jason-watkins/nixie-clock/docs/design_analysis/main.tex

\documentclass[11pt,letterpaper]{article}

% ---------------------------------------------------------------------------
% Nixie Clock -- Design Basis
%
% Derives the board's key electrical characteristics from first principles
% and from component datasheets on file in docs/datasheets/. This document
% works at the schematic level only; it is the source from which the
% eventual Hardware User Guide's tables are extracted.
% ---------------------------------------------------------------------------

\usepackage[letterpaper,margin=1in]{geometry}

% Project-local fonts (PT Serif for text, IBM Plex Mono for monospace; both
% carry Latin and Cyrillic, are OFL-licensed, and are committed under fonts/ so
% the build has no system-font dependency). Requires XeLaTeX or LuaLaTeX --
% fontspec does not work under pdfLaTeX.
\usepackage{fontspec}
\setmainfont{PTSerif}[
  Path = fonts/,
  Extension = .ttf,
  UprightFont = *-Regular,
  BoldFont = *-Bold,
  ItalicFont = *-Italic,
  BoldItalicFont = *-BoldItalic,
]
% Plex Mono sets a shade larger than PT Serif at the same nominal size;
% MatchLowercase equalises the x-heights, trimming about 3 percent, so inline
% \texttt does not read oversized against the surrounding text.
\setmonofont{IBMPlexMono}[
  Path = fonts/,
  Extension = .ttf,
  UprightFont = *-Regular,
  BoldFont = *-Bold,
  Scale = MatchLowercase,
]

\usepackage{amsmath,amssymb}
\usepackage{siunitx}
\usepackage{booktabs}
\usepackage{longtable}
\usepackage{array}
\usepackage{multirow}
\usepackage{graphicx}
\usepackage{enumitem}
\usepackage[colorlinks=true,linkcolor=blue,citecolor=blue,urlcolor=blue]{hyperref}
\usepackage{cleveref}
\usepackage{chngcntr}

% Tables number "<section>-<n>" (e.g. 2-1, 2-2, 3-1), resetting only at
% each \section, not at \subsection -- a table living inside a particular
% subsection is incidental to this scheme, not what it counts by.
\counterwithin{table}{section}
\renewcommand{\thetable}{\thesection-\arabic{table}}
\counterwithin{figure}{section}
\renewcommand{\thefigure}{\thesection-\arabic{figure}}

\graphicspath{{figures/}}

% Reference designators are set the way the schematics draw them: a class
% letter carrying a subsystem-and-function tag as an upright subscript.
% \des{R}{3V3D1} -> R_3V3D1. Works in prose and inside math alike, and
% degrades to a flat "R_3V3D1" in PDF bookmarks, where math is unavailable.
\newcommand{\des}[2]{\texorpdfstring{\ensuremath{#1_{\mathrm{#2}}}}{#1\_#2}}

% Number down to \paragraph (depth 4) so a deeply nested topic -- e.g. one
% pin's check inside a "housekeeping" subsubsection -- still gets its own
% citable number instead of forcing an ever-larger subsubsection to do the
% job of several independent ones. article's default tocdepth already
% reaches this depth, so paragraph headings appear in the ToC too.
\setcounter{secnumdepth}{4}
\crefname{paragraph}{paragraph}{paragraphs}
\Crefname{paragraph}{Paragraph}{Paragraphs}

\sisetup{
  per-mode = symbol,
  detect-all = true,
  table-align-text-post = false,
}

% Consistent units used throughout
\DeclareSIUnit\decade{decade}

% Shorthand for a datasheet citation inside table cells and prose.
% Usage: \ds{SN74141\_TI.pdf}{2}
\newcommand{\ds}[2]{\textit{#1}, p.~#2}

\newcolumntype{L}[1]{>{\raggedright\arraybackslash}p{#1}}

% \DesignRev is generated by scripts/make_release.py --sync-doc-rev from
% the KiCad project's REV text variable -- do not hand-edit revision.tex.
\input{revision}

\title{Nixie Clock: Design Basis}
\author{}
\date{Rev \DesignRev{}, compiled \today}

\begin{document}
\maketitle

\begin{abstract}
\noindent
This document derives the main electrical characteristics of the Nixie Clock
board. It uses component datasheets and circuit analysis. The analysis applies
at the schematic level. Package data applies only when a part is available in
one package. Each numerical value for a critical component has a datasheet
reference in \texttt{docs/datasheets/}. Other component values use standard
engineering practice. The analysis starts at the Nixie-tube load. It then
derives the 170~V, 5~V, and 3.3~V supplies. The final section derives the
USB-PD input stage.
\end{abstract}

\tableofcontents
\listoftables
\listoffigures

\input{sections/01_introduction}
\input{sections/02_tubes}
\input{sections/03_bcd_driver}
\input{sections/04_hv_components}
\input{sections/05_hv_converter}
\input{sections/06_lv_components}
\input{sections/07_esp32}
\input{sections/08_5v_converter}
\input{sections/09_3v3_converter}
\input{sections/10_usb_pd}

\end{document}
