jason-watkins/nixie-clock/docs/design_analysis/schematics/3v3.kicad_sch

## KiCad design docs/design_analysis/schematics/3v3.kicad_sch (2026-07-31)

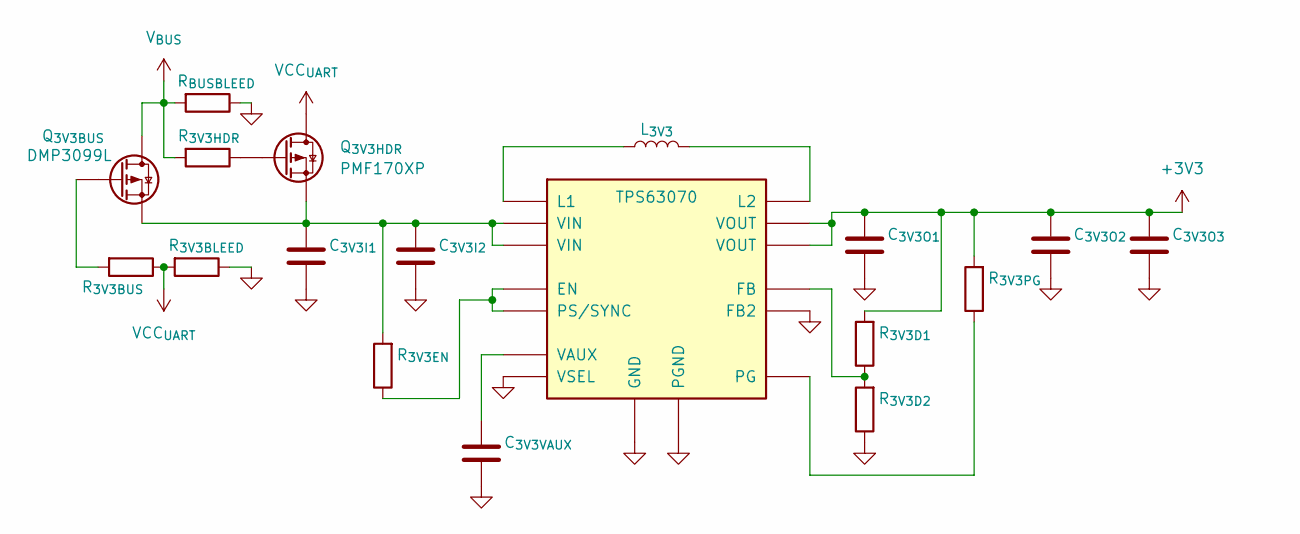
[picture p26: schematic 3v3.kicad_sch]

Parts:
C_{3V3I1}: 10uF; C_0805_2012Metric; MFG Part No CL21A106KAYNNNE; LCSC C15850
C_{3V3I2}: 10uF; C_0603_1608Metric; MFG Part No CL10A106MA8NRNC; LCSC C96446
C_{3V3O1}: 10uF; C_0603_1608Metric; MFG Part No CL10A226MQ8NRNC; LCSC C59461
C_{3V3O2}: 22uF; C_1206_3216Metric; MFG Part No CL31A226KPHNNNE; LCSC C5672
C_{3V3O3}: 47uF; C_1206_3216Metric; MFG Part No CL31A476MPHNNNE; LCSC C96123
C_{3V3VAUX}: 100nF; C_0402_1005Metric; MFG Part No CL05B104KO5NNNC; LCSC C1525
L_{3V3}: 1.5uH; L_Bourns_SRN5040TA; MFG Part No SRN5040TA-1R5M
Q_{3V3BUS}: DMP3099L; SOT-323_SC-70; MFG Part No PMF170XP,115
Q_{3V3HDR}: PMF170XP; SOT-323_SC-70; MFG Part No PMF170XP,115
R_{3V3BLEED}, R_{3V3BUS}, R_{3V3HDR}, R_{3V3PG}: 100k; R_0402_1005Metric; MFG Part No 0402WGF1003TCE; LCSC C25741
R_{3V3D1}: 120k; R_0402_1005Metric; MFG Part No 0402WGF1203TCE; LCSC C25750
R_{3V3D2}: 39k; R_0402_1005Metric; MFG Part No 0402WGF5102TCE; LCSC C25794
R_{3V3EN}: 10k; R_0402_1005Metric; MFG Part No 0402WGF1002TCE; LCSC C25744
R_{BUSBLEED}: 100k; R_0402_1005Metric; MFG Part No 0402WGF1003TCE; LCSC C25741
U302: TPS63070; VQFN-15_2.5x3mm_TI_RNM0015A; MFG Part No TPS630702RNMR

Connections:
+3V3: C_{3V3O1}.1, C_{3V3O2}.1, C_{3V3O3}.1, R_{3V3D1}.2, R_{3V3PG}.2, U302.7 (VOUT), U302.8 (VOUT)
GND: C_{3V3I1}.2, C_{3V3I2}.2, C_{3V3O1}.2, C_{3V3O2}.2, C_{3V3O3}.2, C_{3V3VAUX}.2, R_{3V3BLEED}.1, R_{3V3D2}.1, R_{BUSBLEED}.1, U302.4 (GND), U302.6 (FB2), U302.10 (PGND), U302.15 (VSEL)
unnamed: C_{3V3I1}.1, C_{3V3I2}.1, Q_{3V3BUS}.2 (S), Q_{3V3HDR}.2 (S), R_{3V3EN}.2, U302.12 (VIN), U302.13 (VIN)
unnamed: C_{3V3VAUX}.1, U302.3 (VAUX)
unnamed: L_{3V3}.1, U302.11 (L1)
unnamed: L_{3V3}.2, U302.9 (L2)
unnamed: Q_{3V3BUS}.1 (G), R_{3V3BUS}.2
unnamed: Q_{3V3HDR}.1 (G), R_{3V3HDR}.1
unnamed: R_{3V3D1}.1, R_{3V3D2}.2, U302.5 (FB)
unnamed: R_{3V3EN}.1, U302.1 (PS/SYNC), U302.14 (EN)
unnamed: R_{3V3PG}.1, U302.2 (PG)
VCC_{UART}: Q_{3V3HDR}.3 (D), R_{3V3BLEED}.2, R_{3V3BUS}.1
V_{BUS}: Q_{3V3BUS}.3 (D), R_{3V3HDR}.2, R_{BUSBLEED}.2
