jason-watkins/nixie-clock/docs/design_analysis/schematics/5v.kicad_sch

## KiCad design docs/design_analysis/schematics/5v.kicad_sch (2026-07-29)

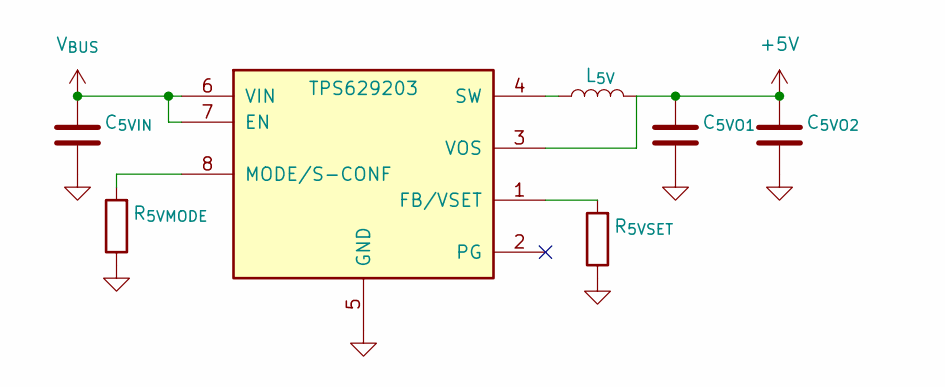
[picture p27: schematic 5v.kicad_sch]

Parts:
C_{5VIN}: 10uF; C_0805_2012Metric; MFG Part No CL21A106KAYNNNE; LCSC C15850
C_{5VO1}, C_{5VO2}: 22uF; C_1206_3216Metric; MFG Part No CL31A226KPHNNNE; LCSC C5672
L_{5V}: 2.2uH; L_Bourns_SRN5040TA; MFG Part No SRN5040TA-2R2M
R_{5VMODE}: 27k; R_0402_1005Metric; MFG Part No 0402WGF2702TCE; LCSC C25771
R_{5VSET}: 80.6k; R_0402_1005Metric; MFG Part No 0402WGF7502TCE; LCSC C25798
U303: TPS629203; SOT-583-8; MFG Part No TPS629203DRLR

Connections:
+5V: C_{5VO1}.1, C_{5VO2}.1, L_{5V}.2, U303.3 (VOS)
GND: C_{5VIN}.2, C_{5VO1}.2, C_{5VO2}.2, R_{5VMODE}.1, R_{5VSET}.1, U303.5 (GND)
unnamed: L_{5V}.1, U303.4 (SW)
unnamed: R_{5VMODE}.2, U303.8 (MODE/S-CONF)
unnamed: R_{5VSET}.2, U303.1 (FB/VSET)
V_{BUS}: C_{5VIN}.1, U303.6 (VIN), U303.7 (EN)
