jason-watkins/nixie-clock/docs/design_analysis/schematics/hv.kicad_sch

## KiCad design docs/design_analysis/schematics/hv.kicad_sch (2026-07-29)

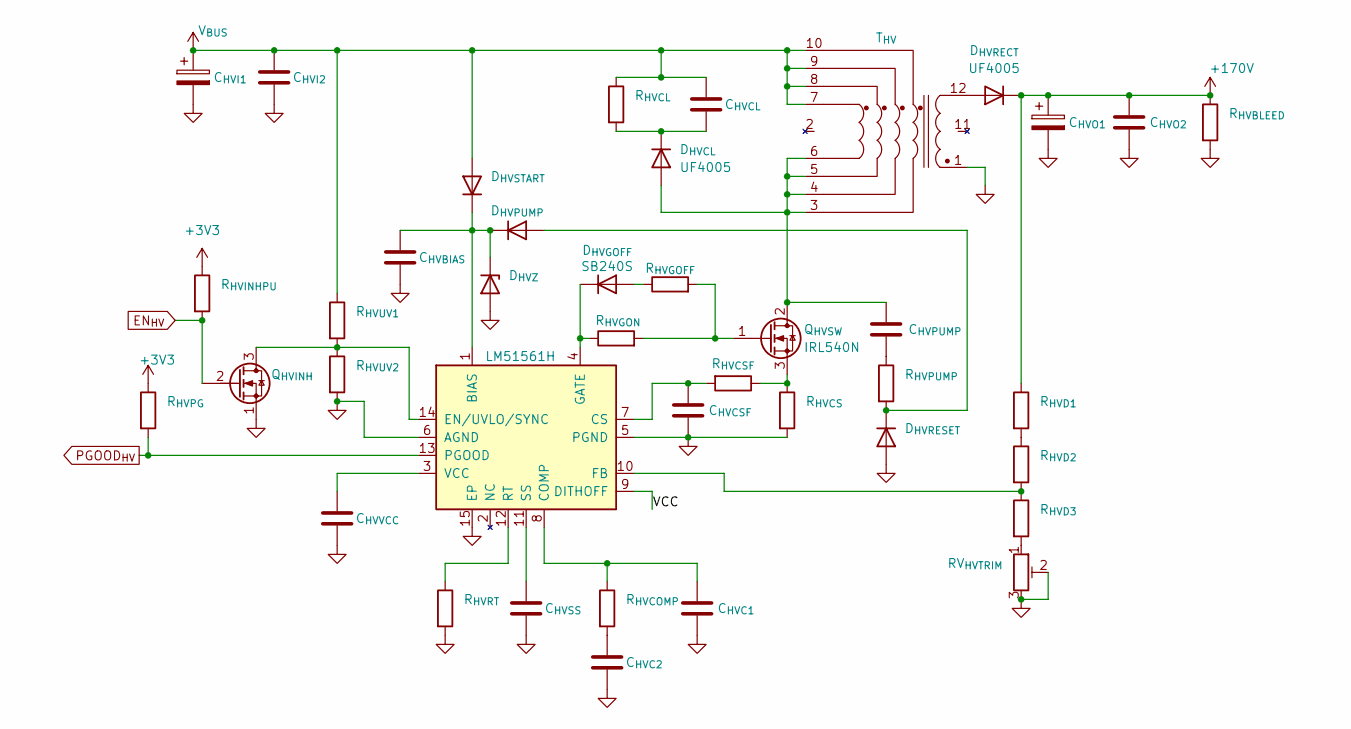
[picture p28: schematic hv.kicad_sch]

Parts:
C_{HVBIAS}: 1uF; C_Rect_L5.1mm_W3.2mm_P5.08mm_Goldmax; MFG Part No C322C103K5R5TA
C_{HVC1}: 220pF; C_Rect_L5.1mm_W3.2mm_P5.08mm_Goldmax; MFG Part No C322C221K5R5TA
C_{HVC2}: 100nF; C_Rect_L5.1mm_W3.2mm_P5.08mm_Goldmax; MFG Part No C322C104K5R5TA
C_{HVCL}: 12nF; C_Rect_L3.8mm_W2.5mm_P5.08mm_Goldmax; MFG Part No C317C123K1R5TA7301
C_{HVCSF}: 470pF; C_Rect_L3.8mm_W2.5mm_P2.54mm_Goldmax; MFG Part No C315C471K5R5TA
C_{HVI1}: 100uF; CP_Radial_D8.0mm_P3.50mm; MFG Part No A750KK107M1EAAE040
C_{HVI2}: 4.7uF; C_Rect_L5.1mm_W3.2mm_P5.08mm_Goldmax; MFG Part No C322C475K5R5TA
C_{HVO1}: 4.7uF; CP_Radial_D8.0mm_P3.50mm; MFG Part No A759KS475M2EAAE496
C_{HVO2}: 100nF; C_Rect_L7.9mm_W5.9mm_P5.00mm_ECQE; MFG Part No ECQ-E2104KB
C_{HVPUMP}: 4.7nF
C_{HVSS}: 220nF; C_Rect_L5.1mm_W3.2mm_P5.08mm_Goldmax; MFG Part No C322C224K5R5TA7301
C_{HVVCC}: 2.2uF; C_Rect_L5.1mm_W3.2mm_P5.08mm_Goldmax; MFG Part No C322C225K5R5TA
D_{HVCL}: UF4005; D_DO-41_SOD81_P7.62mm_Horizontal; MFG Part No UF4005
D_{HVGOFF}: SB240S; D_DO-41_SOD81_P7.62mm_Horizontal; MFG Part No SB240S-E3/54
D_{HVPUMP}: D
D_{HVRECT}: UF4005; D_DO-41_SOD81_P10.16mm_Horizontal; MFG Part No UF4005
D_{HVRESET}: D
D_{HVSTART}: D
D_{HVZ}: D_Zener
Q_{HVINH}: TN2106N3-G; TO-92L; MFG Part No TN2106N3-G
Q_{HVSW}: IRL540N; TO-220-3_Vertical; MFG Part No IRL540NPBF
RV_{HVTRIM}: 3296; Potentiometer_Bourns_3296W_Vertical; MFG Part No 3296W-1-202LF
R_{HVBLEED}: 1.5M; R_Axial_DIN0207_L6.3mm_D2.5mm_P7.62mm_Horizontal; MFG Part No MFR-25FBF52-1M5
R_{HVCL}: 30k; R_Axial_DIN0207_L6.3mm_D2.5mm_P7.62mm_Horizontal; MFG Part No MFR-25FRF52-30K
R_{HVCOMP}: 10k; R_Axial_DIN0207_L6.3mm_D2.5mm_P7.62mm_Horizontal; MFG Part No MFR-25FRF52-10K
R_{HVCSF}: 100; R_Axial_DIN0207_L6.3mm_D2.5mm_P7.62mm_Horizontal; MFG Part No MFR-25FBF52-100R
R_{HVCS}: 39m; R_2512_6332Metric_Pad1.40x3.35mm_HandSolder; MFG Part No TLRP3A20WR039FTE
R_{HVD1}, R_{HVD2}: 866k; R_Axial_DIN0207_L6.3mm_D2.5mm_P7.62mm_Horizontal; MFG Part No MFR-25FRF52-866K
R_{HVD3}: 8.87k; R_Axial_DIN0207_L6.3mm_D2.5mm_P7.62mm_Horizontal; MFG Part No MFR-25FBF52-8K87
R_{HVGOFF}: 3.3; R_Axial_DIN0207_L6.3mm_D2.5mm_P7.62mm_Horizontal; MFG Part No MFR-25FTE52-3R3
R_{HVGON}: 10; R_Axial_DIN0207_L6.3mm_D2.5mm_P7.62mm_Horizontal; MFG Part No MFR-25FBF52-10R
R_{HVINHPU}: 100k; R_Axial_DIN0207_L6.3mm_D2.5mm_P7.62mm_Horizontal; MFG Part No MFR-25FRF52-100K
R_{HVPG}: 100k; R_Axial_DIN0207_L6.3mm_D2.5mm_P7.62mm_Horizontal; MFG Part No MFR-25FRF52-100K
R_{HVPUMP}: 82
R_{HVRT}: 147k; R_Axial_DIN0207_L6.3mm_D2.5mm_P7.62mm_Horizontal; MFG Part No MFR-25FRF52-147K
R_{HVUV1}: 63.4k; R_Axial_DIN0207_L6.3mm_D2.5mm_P7.62mm_Horizontal; MFG Part No MFR-25FRF52-143K
R_{HVUV2}: 32.4k; R_Axial_DIN0207_L6.3mm_D2.5mm_P7.62mm_Horizontal; MFG Part No MFR-25FRF52-32K4
T_{HV}: DA2032-AL; MFG Part No DA2032-AL
U2: LM51561H; Texas_HTSSOP-14-1EP_4.4x5mm_P0.65mm_EP3.4x5mm_Mask3.155x3.2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; MFG Part No LM51561HPWPR

Connections:
+3V3: R_{HVINHPU}.1, R_{HVPG}.1
+170V: C_{HVO1}.1, C_{HVO2}.1, D_{HVRECT}.1 (K), R_{HVBLEED}.1, R_{HVD1}.1
EN_{HV}: Q_{HVINH}.2 (G), R_{HVINHPU}.2
GND: C_{HVBIAS}.1, C_{HVC1}.1, C_{HVC2}.1, C_{HVCSF}.1, C_{HVI1}.2, C_{HVI2}.2, C_{HVO1}.2, C_{HVO2}.2, C_{HVSS}.1, C_{HVVCC}.1, D_{HVRESET}.2 (A), D_{HVZ}.2 (A), Q_{HVINH}.1 (S), RV_{HVTRIM}.2, RV_{HVTRIM}.3, R_{HVBLEED}.2, R_{HVCS}.2, R_{HVRT}.2, R_{HVUV2}.2, T_{HV}.1, U2.5 (PGND), U2.6 (AGND), U2.15 (EP)
unnamed: C_{HVBIAS}.2, D_{HVPUMP}.1 (K), D_{HVSTART}.1 (K), D_{HVZ}.1 (K), U2.1 (BIAS)
unnamed: C_{HVC1}.2, R_{HVCOMP}.1, U2.8 (COMP)
unnamed: C_{HVC2}.2, R_{HVCOMP}.2
unnamed: C_{HVCL}.1, D_{HVCL}.1 (K), R_{HVCL}.2
unnamed: C_{HVCSF}.2, R_{HVCSF}.2, U2.7 (CS)
unnamed: C_{HVPUMP}.1, D_{HVCL}.2 (A), Q_{HVSW}.2 (D), T_{HV}.3, T_{HV}.4, T_{HV}.5, T_{HV}.6
unnamed: C_{HVPUMP}.2, R_{HVPUMP}.1
unnamed: C_{HVSS}.2, U2.11 (SS)
unnamed: C_{HVVCC}.2, U2.3 (VCC)
unnamed: D_{HVGOFF}.1 (K), R_{HVGON}.1, U2.4 (GATE)
unnamed: D_{HVGOFF}.2 (A), R_{HVGOFF}.1
unnamed: D_{HVPUMP}.2 (A), D_{HVRESET}.1 (K), R_{HVPUMP}.2
unnamed: D_{HVRECT}.2 (A), T_{HV}.12
unnamed: Q_{HVINH}.3 (D), R_{HVUV1}.2, R_{HVUV2}.1, U2.14 (EN/UVLO/SYNC)
unnamed: Q_{HVSW}.1 (G), R_{HVGOFF}.2, R_{HVGON}.2
unnamed: Q_{HVSW}.3 (S), R_{HVCSF}.1, R_{HVCS}.1
unnamed: RV_{HVTRIM}.1, R_{HVD3}.2
unnamed: R_{HVD1}.2, R_{HVD2}.1
unnamed: R_{HVD2}.2, R_{HVD3}.1, U2.10 (FB)
unnamed: R_{HVRT}.1, U2.12 (RT)
PGOOD_{HV}: R_{HVPG}.2, U2.13 (PGOOD)
VCC: U2.9 (DITHOFF)
V_{BUS}: C_{HVCL}.2, C_{HVI1}.1, C_{HVI2}.1, D_{HVSTART}.2 (A), R_{HVCL}.1, R_{HVUV1}.1, T_{HV}.7, T_{HV}.8, T_{HV}.9, T_{HV}.10
