jason-watkins/nixie-clock/docs/design_analysis/schematics/mcu.kicad_sch

## KiCad design docs/design_analysis/schematics/mcu.kicad_sch (2026-07-29)

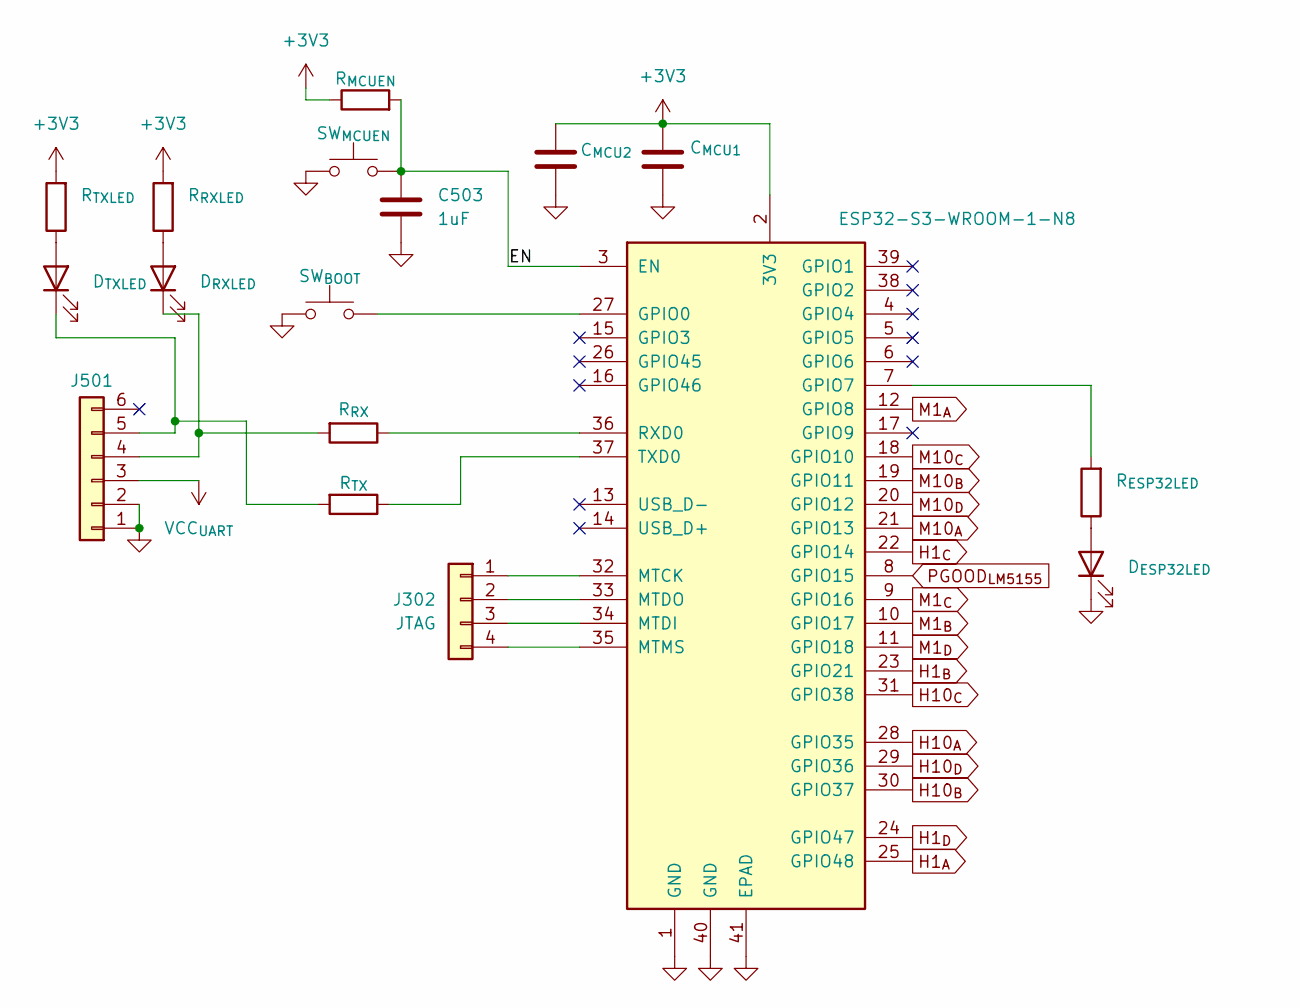
[picture p29: schematic mcu.kicad_sch]

Parts:
C503: 1uF; C_0805_2012Metric_Pad1.18x1.45mm_HandSolder; MFG Part No C0805C105K3RACTU
C_{MCU1}: 100nF; C_0805_2012Metric_Pad1.18x1.45mm_HandSolder; MFG Part No C0805C104K3RACTU
C_{MCU2}: 22uF; C_0805_2012Metric_Pad1.18x1.45mm_HandSolder; MFG Part No GMC21X5R226M25NT
D_{ESP32LED}: HB; LED_0805_2012Metric_Pad1.15x1.40mm_HandSolder; MFG Part No LTST-C171GKT
D_{RXLED}: TX; LED_0805_2012Metric_Pad1.15x1.40mm_HandSolder; MFG Part No LTST-C171GKT
D_{TXLED}: RX; LED_0805_2012Metric_Pad1.15x1.40mm_HandSolder; MFG Part No LTST-C171GKT
J302: JTAG; PinHeader_1x04_P2.54mm_Vertical
J501: UART; PinHeader_1x06_P2.54mm_Vertical
R_{ESP32LED}: 1.5k; R_0805_2012Metric_Pad1.20x1.40mm_HandSolder; MFG Part No RMCF0805FT1K5
R_{MCUEN}: 10k; R_0805_2012Metric_Pad1.20x1.40mm_HandSolder; MFG Part No RMCF0805FT10K0
R_{RXLED}: 1.5k; R_0805_2012Metric_Pad1.20x1.40mm_HandSolder; MFG Part No RMCF0805FT1K5
R_{RX}: 1k; R_0805_2012Metric_Pad1.20x1.40mm_HandSolder; MFG Part No RMCF0805FT1K
R_{TXLED}: 1.5k; R_0805_2012Metric_Pad1.20x1.40mm_HandSolder; MFG Part No RMCF0805FT1K5
R_{TX}: 1k; R_0805_2012Metric_Pad1.20x1.40mm_HandSolder; MFG Part No RMCF0805FT1K
SW_{BOOT}: Boot; SW_Panasonic_EVQ_4.9x4.9mm; MFG Part No EVQ-PT9A15
SW_{MCUEN}: Reset; SW_Panasonic_EVQ_4.9x4.9mm; MFG Part No EVQ-PT9A15
U501: ESP32-S3-WROOM-1-N8; ESP32-S3-WROOM-1; MFG Part No ESP32-S3-WROOM-1-N8

Connections:
+3V3: C_{MCU1}.1, C_{MCU2}.1, R_{MCUEN}.1, R_{RXLED}.2, R_{TXLED}.2, U501.2 (3V3)
EN: C503.1, R_{MCUEN}.2, SW_{MCUEN}.2, U501.3 (EN)
GND: C503.2, C_{MCU1}.2, C_{MCU2}.2, D_{ESP32LED}.1 (K), J501.1, J501.2, SW_{BOOT}.1, SW_{MCUEN}.1, U501.1 (GND), U501.40 (GND), U501.41 (EPAD)
H1_{A}: U501.25 (GPIO48)
H1_{B}: U501.23 (GPIO21)
H1_{C}: U501.22 (GPIO14)
H1_{D}: U501.24 (GPIO47)
H10_{A}: U501.28 (GPIO35)
H10_{B}: U501.30 (GPIO37)
H10_{C}: U501.31 (GPIO38)
H10_{D}: U501.29 (GPIO36)
M1_{A}: U501.12 (GPIO8)
M1_{B}: U501.10 (GPIO17)
M1_{C}: U501.9 (GPIO16)
M1_{D}: U501.11 (GPIO18)
M10_{A}: U501.21 (GPIO13)
M10_{B}: U501.19 (GPIO11)
M10_{C}: U501.18 (GPIO10)
M10_{D}: U501.20 (GPIO12)
unnamed: D_{ESP32LED}.2 (A), R_{ESP32LED}.1
unnamed: D_{RXLED}.1 (K), J501.4, R_{RX}.2
unnamed: D_{RXLED}.2 (A), R_{RXLED}.1
unnamed: D_{TXLED}.1 (K), J501.5, R_{TX}.2
unnamed: D_{TXLED}.2 (A), R_{TXLED}.1
unnamed: J302.1, U501.32 (MTCK)
unnamed: J302.2, U501.33 (MTDO)
unnamed: J302.3, U501.34 (MTDI)
unnamed: J302.4, U501.35 (MTMS)
unnamed: R_{ESP32LED}.2, U501.7 (GPIO7)
unnamed: R_{RX}.1, U501.36 (RXD0)
unnamed: R_{TX}.1, U501.37 (TXD0)
unnamed: SW_{BOOT}.2, U501.27 (GPIO0)
PGOOD_{LM5155}: U501.8 (GPIO15)
VCC_{UART}: J501.3
