jason-watkins/nixie-clock/docs/design_analysis/schematics/usbpd.kicad_sch

## KiCad design docs/design_analysis/schematics/usbpd.kicad_sch (2026-07-29)

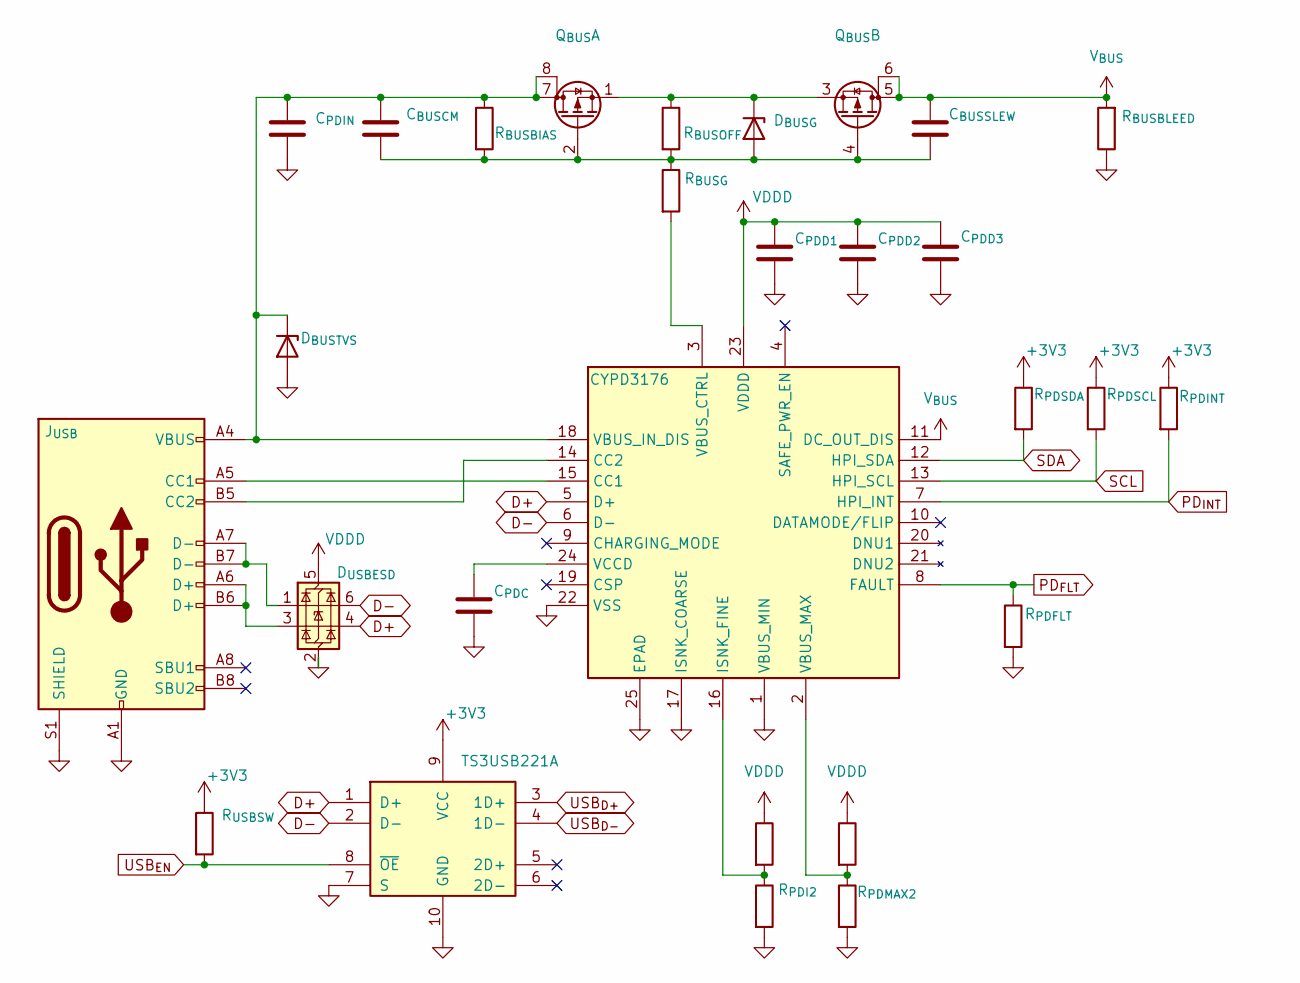
[picture p30: schematic usbpd.kicad_sch]

Parts:
C_{BUSCM}: 1uF; C_0603_1608Metric
C_{BUSSLEW}: 1uF; C_0603_1608Metric
C_{PDC}: 1uF; C_0603_1608Metric
C_{PDD1}: 1uF; C_0603_1608Metric
C_{PDD2}, C_{PDD3}: 100nF; C_0402_1005Metric
C_{PDIN}: 100nF; C_0603_1608Metric
D_{BUSG}: SD15Q-7; D_SOD-323; MFG Part No SD15Q-7; LCSC C19950473
D_{BUSTVS}: SD15Q-7; D_SOD-323; MFG Part No SD15Q-7; LCSC C19950473
D_{USBESD}: USBLC6-2
J_{USB}: (no value)
Q_{BUS}: Q_Dual_PMOS_S1G1S2G2D2D2D1D1; SOIC-8_3.9x4.9mm_P1.27mm; MFG Part No DMP3085LSD-13
R_{BUSBIAS}: 49.9k; R_0402_1005Metric
R_{BUSBLEED}: R_0402_1005Metric
R_{BUSG}: 100; R_0402_1005Metric
R_{BUSOFF}: 49.9k; R_0402_1005Metric
R_{PDFLT}: 100k; R_0402_1005Metric
R_{PDI1}: 5.1k; R_0402_1005Metric
R_{PDI2}: 2.4k; R_0402_1005Metric
R_{PDINT}: 10k; R_0402_1005Metric
R_{PDMAX1}: 5.1k; R_0402_1005Metric
R_{PDMAX2}: 2.4k; R_0402_1005Metric
R_{PDSCL}: 10k; R_0402_1005Metric
R_{PDSDA}: 10k; R_0402_1005Metric
R_{USBSW}: 10k; R_0402_1005Metric
U102: TS3USB221A
U304: CYPD3176

Connections:
+3V3: R_{PDINT}.1, R_{PDSCL}.1, R_{PDSDA}.1, R_{USBSW}.1, U102.9 (VCC)
D+: D_{USBESD}.4 (I/O2), U102.1 (D+), U304.5 (D+)
D-: D_{USBESD}.6 (I/O1), U102.2 (D-), U304.6 (D-)
GND: C_{PDC}.2, C_{PDD1}.2, C_{PDD2}.2, C_{PDD3}.2, C_{PDIN}.2, D_{BUSTVS}.2 (A), D_{USBESD}.2 (GND), J_{USB}.A1 (GND), J_{USB}.A12 (GND), J_{USB}.B1 (GND), J_{USB}.B12 (GND), J_{USB}.S1 (SHIELD), R_{BUSBLEED}.1, R_{PDFLT}.2, R_{PDI2}.2, R_{PDMAX2}.2, U102.7 (S), U102.10 (GND), U304.1 (VBUS_MIN), U304.17 (ISNK_COARSE), U304.22 (VSS), U304.25 (EPAD)
unnamed: C_{BUSCM}.1, C_{PDIN}.1, D_{BUSTVS}.1 (K), J_{USB}.A4 (VBUS), J_{USB}.A9 (VBUS), J_{USB}.B4 (VBUS), J_{USB}.B9 (VBUS), Q_{BUS}.7 (D), Q_{BUS}.8 (D), R_{BUSBIAS}.1, U304.18 (VBUS_IN_DIS)
unnamed: C_{BUSCM}.2, C_{BUSSLEW}.2, D_{BUSG}.2 (A), Q_{BUS}.2 (G), Q_{BUS}.4 (G), R_{BUSBIAS}.2, R_{BUSG}.1, R_{BUSOFF}.2
unnamed: C_{PDC}.1, U304.24 (VCCD)
unnamed: D_{BUSG}.1 (K), Q_{BUS}.1 (S), Q_{BUS}.3 (S), R_{BUSOFF}.1
unnamed: D_{USBESD}.1 (I/O1), J_{USB}.A7 (D-), J_{USB}.B7 (D-)
unnamed: D_{USBESD}.3 (I/O2), J_{USB}.A6 (D+), J_{USB}.B6 (D+)
unnamed: J_{USB}.A5 (CC1), U304.15 (CC1)
unnamed: J_{USB}.B5 (CC2), U304.14 (CC2)
unnamed: R_{BUSG}.2, U304.3 (VBUS_CTRL)
unnamed: R_{PDI1}.2, R_{PDI2}.1, U304.16 (ISNK_FINE)
unnamed: R_{PDMAX1}.2, R_{PDMAX2}.1, U304.2 (VBUS_MAX)
PD_{FLT}: R_{PDFLT}.1, U304.8 (FAULT)
PD_{INT}: R_{PDINT}.2, U304.7 (HPI_INT)
SCL: R_{PDSCL}.2, U304.13 (HPI_SCL)
SDA: R_{PDSDA}.2, U304.12 (HPI_SDA)
USB_{D+}: U102.3 (1D+)
USB_{D-}: U102.4 (1D-)
USB_{EN}: R_{USBSW}.2, U102.8 (~OE)
VDDD: C_{PDD1}.1, C_{PDD2}.1, C_{PDD3}.1, D_{USBESD}.5 (VBUS), R_{PDI1}.1, R_{PDMAX1}.1, U304.23 (VDDD)
V_{BUS}: C_{BUSSLEW}.1, Q_{BUS}.5 (D), Q_{BUS}.6 (D), R_{BUSBLEED}.2, U304.11 (DC_OUT_DIS)
